pythagorean-comma/cv-module/docs/ASSUMPTIONS.md

# ASSUMPTIONS.md

Everything in this repo that had to be guessed, and what each guess costs if it is wrong.

Generated by `gen_assumptions.py`. The numeric entries are pulled from the code — `design.MEASURED`, `design.UNSPECIFIED`, `design.DEFERRED`, `contract.socket.ADAPTED` and `gen_bom.PRICES` — so a guess cannot be resolved in one place and left standing here. The rest are declared in that file, because a reading of a sentence does not fit in a dict of floats.

The discipline is the mixer's. Its `Assumption` class says it plainly: **the range matters more than the value.** The value is a guess; the range is a claim about what the design survives, and `check_assumptions()` fails the build if a value ever falls outside the range it was written around.

## The short version

**One entry would change the board; the rest would change a number:**

1. **`MEASURED['noise_floor']`** — the mixer's own unmeasured figure, which decides whether this module costs 0.11 dB or 0.85 dB with everything open, and 0.56 dB or 3.17 dB while the lead feature is running.

**The pad relay was the second and it is not an assumption any more.** It was the largest unchosen part in the design — 52 % of the placed courtyard, about two thirds of the BOM — and rather than being chosen it has been deleted, along with the pad it switched. `design.pad_benefit()` prices the pad against the control port that replaces it and the answer is 0.000 dB of system noise at every noise floor in the declared range. Nothing here is waiting on a relay.

**Two entries that *were* on this list are settled rather than open.** Constraint 2's "six separate returns" has been struck, with the arithmetic, in [Readings of the spec](#readings-of-the-spec). And the 20.2 µF that used to sit on VREF — twice the MAX6126's capacitive-load stability ceiling, because two 10 µF reservoirs were fitted — is resolved by deleting C804: its justification was shielding the reference's loop from an 8 kHz load step, and at 8 kHz a 10 µF could only supply 1.4 % of that step. VREF now carries 10.2 µF, which is the datasheet's own recommended 10 µF ∥ 0.1 µF, and `verify.check_reference_load()` holds the range against KiCad's netlist. See `design.reference_load()`.

## Numbers with declared ranges

From `design.MEASURED`, which is the mixer's `Assumption` class reused rather than reimplemented.

**8 of these are worth a bench and 2 are not**, and the difference is computed rather than felt. `design.SETTLED` names the ones whose *whole declared range* gives the same answer, and `design.check_settled()` recomputes that on every build — so a retirement expires the day the design makes one load-bearing again. Both of the retired ones are barrier residuals: at their joint worst corner, against the **optimistic** end of `noise_floor`'s own range, they put 4.09 µV at the audio bond, which is -21.8 dB — 1.8 dB inside the 20 dB the check holds, with three worst cases stacked.

### `cv_corner` = 254.7 Hz, 2-pole

**Range:** 200.0 .. 400.0

**Question:** Is a 250 Hz CV filter fast enough for the gate feel? Open question 5 in 00-current-state.md, and it is a judgement by ear rather than a measurement.

**Sets:** the anti-AM filtering, the de-click, and how the gate feels

**When wrong:** Two capacitors per channel. The corner scales as 1/C with the resistors fixed at the <=22k the noise budget wants, so 400 Hz is C1 = 36n / C2 = 15n and nothing else moves. Note the direction of the trade: faster is a worse anti-AM filter and a sharper click, and 00-current-state puts this block at 15-20 dB of the whole noise argument.

### `dcdc_node_v` = 40.0 V pk-pk, flyback primary switching node — **retired**

**Retired, and still a guess:** barrier_return() scales linearly with it, so the whole 24-72 V range moves the residual at the audio bond from 0.69 to 2.06 uV -- 46.4 dB to 36.9 dB *under* the mixer's own noise floor. There is no value in the range at which another part is worth fitting, which is the only decision it feeds.

**Range:** 24.0 .. 72.0

**Question:** How large is the swing on the TMR 6WI's primary switching node? A flyback's drain sits at Vin plus the reflected output, so at a 12-18 V input the range below is 2x to 4x the input -- read off what the topology permits, not off the datasheet, which does not say.

**Sets:** the common-mode current through the 50 pF barrier, and with it the size of the Y-capacitor

**When wrong:** Linearly. barrier_return() scales with it, so the top of the range is 5 dB worse than the value and the bottom is 4 dB better -- and the *fraction* returned locally does not move at all, because it is set by two impedances. What would change is whether the residual at the bond is worth another part, and at every point in this range it is not.

### `inlet_loop_uh` = 0.75 uH, the loop the shared inlet closes — **retired**

**Retired, and still a guess:** It used to be the denominator of a split and is a straight scale now: L801 puts 3.6 kohm in that denominator, so 0.3 and 1.5 uH return the same 99.984 % locally to five figures and differ only in the residual, 0.47 to 2.27 uV. **The choke is what retired it** -- before it was fitted the range mattered and the assumption's own when_wrong named a choke as the fix.

**Range:** 0.3 .. 1.5

**Question:** What is the inductance of the loop formed by the audio ground bond, the mixer's own AGND/PGND star, and the two inlet leads back to the shared barrel jack? It is a property of how the box is wired, not of either board.

**Sets:** the impedance of the bond the barrier's residual current is developed across

**When wrong:** **Re-read after L801 was fitted, and it is a different assumption now.** It used to be the *denominator of a split* -- barrier_return() divided the barrier current between C810 and this loop, so a smaller loop was a worse result and the whole declared range mattered. The choke puts 3.6 kohm in that denominator, so the split is set by the part and not by the box: 0.3 and 1.5 uH give the same 99.98 % local return to four figures. What is left is a straight scale on the residual, because the bond voltage is this impedance times a current that no longer depends on it -- a factor of 5 across the range, on 1.1 uV that is 42 dB under the mixer's own noise floor. Every point in the range is inaudible and so is every point outside it. The old clause named a choke as the answer if the number went the wrong way; the choke is fitted, so the question this assumption asks has stopped being load-bearing. **Retired: it is in SETTLED**, and it is the worked example of why that table needs check_settled() beside it -- this was load-bearing until one part went on, and would be again the day it came off.

### `logic_law_error` = 0.0023 fractional, '541 output-impedance asymmetry

**Range:** 0.0005 .. 0.01

**Question:** How different are the 74AHC541's output resistances high and low, at Vcc = 2.5 V? The asymmetry is a duty-dependent non-linearity in the control law, and the datasheet characterises VOH/VOL at 3.3 V and 4.5 V only.

**Sets:** the linearity of dB against code, and nothing else

**When wrong:** Nothing. It is common to all six channels -- same part, matched -- so it is a law error and not a matching error, and 0.23 % over a 61 dB span is 0.14 dB. Calibratable in firmware from a single measured curve if it ever matters.

### `mcu_dcdc_efficiency` = 0.85 fractional, TPS560430XF at 12 V in, 3.3 V out

**Range:** 0.75 .. 0.92

**Question:** What does U22 draw from VA_RAW at this board's real 3.3 V load? SLVSE22B gives efficiency as figures rather than as a table -- section 7.8's curves at 8, 12, 24 and 36 V in -- and a number read off a plotted curve is not a reading. The measurement is one ammeter in series with the switcher's VIN pin.

**Sets:** how much of the converter's remaining 128.2 mA of +Vout the controller costs -- it was the tightest budget on the board and it is not any more, which is what the note below is about

**When wrong:** **Only in one direction, and the threshold moved a long way when the fix it named was taken.** This read 'about 67 %', and the sentence after it named the lever: the 92.7 mA of relay coil V5 made linearly from twelve volts. That lever was pulled -- U22 makes 5 V now and carries the coils -- and it moved two things at once. The headroom before this block went from 35.4 mA to 128.2, because excluding the controller now excludes the coils too; and the coils stopped passing through the module's own converter, so there is no longer one number covering both stages. mcu_supply()'s u22_floor solves it: **53 % with the module at its own pessimistic end**, against a declared range starting at 75. The pessimistic corner fits with 37 mA of +Vout to spare, so what is left here is a confirmation and not a gate.

### `mcu_rail_ma` = 52.1 mA on 3.3 V, RP2040 alone, maximum average

**Range:** 19.2 .. 52.1

**Question:** What does the RP2040 draw on the 3.3 V side in *this* application? Its datasheet's Table 637 measures four use cases rather than specifying a maximum, and none of them is this one: 'Popcorn' is VGA video at 48 MHz and is the heaviest at 52.1 mA (DVDD 16.6 + IOVDD 35.5, worst-case device over temperature), 'BOOTSEL idle' the lightest active at 19.2 mA. This board runs 125 MHz with almost no IO activity -- six PWM at 30.5 kHz, one 10.4 MHz clock -- and XIP from flash, which Table 635 prices at 37.6 uA/MHz on DVDD and which firmware can retire by running from SRAM. The range is the datasheet's own measurements; the value is its top.

**Sets:** nothing, and that is the point -- controller_supply() shows the linear V3V3 chain fails at both ends of this range and a switcher clears both, so no topology decision waits on it

**When wrong:** Only the size of the switcher, not whether there is one. The bound that decides is conservation of energy: a converter's input current is at least vout/vin times its output, so 3.3/12 x 52.1 = 14.3 mA against 35.4 mA of +Vout headroom, and any efficiency above 40 % clears it. Measuring this would size a part; it would not change the topology. **Both halves of that held and the margin did not.** The switcher is fitted and mcu_supply() counts the rest of the rail -- the flash's 25 mA, the MIDI loop, the opto, the pedal -- so the 14.3 mA floor is 23.6 mA and the efficiency that clears it is 67 %, not 40. It still fits and it is the tightest margin on this board.

### `noise_floor` = 0.000144V rms

**Range:** 5e-05 .. 0.0004

**Question:** What is the residual noise at the mono output with the strings damped and LEVEL at maximum, unweighted over 20 kHz?

**Sets:** whether any further noise work on this box is worth doing

**When wrong:** Near the predicted figure means the source model in source.py is right and the summer is already 29 dB below the thing feeding it. Much lower means the assumed coil resistance and rbb' are pessimistic. Much higher means something is wrong that this model does not describe.

### `pico_smps_efficiency` = 0.91 fractional, RT6150 at 4.7 V in, 3.3 V out, PWM

**Range:** 0.86 .. 0.93

**Question:** What does the Pico draw from VSYS at this board's load? DS6150A/B-05 gives efficiency only as plotted curves -- the 'Buck-Boost 3.3V Efficiency, PS/SYNC = H' figure, which is the forced-PWM one this design runs in -- and at 100 mA the VIN = 3.3 V trace sits near 95 % with the 2.4 V trace about three points under it. A number read off a plotted curve is not a reading, and this one is read at a different inductor from the module's. The measurement is one ammeter in series with the Pico's VSYS pin, with GPIO23 high.

**Sets:** what the module's own 3.3 V load costs +Vout, which is 43 % of what U22 delivers -- see mcu_supply()

**When wrong:** **It is not a threshold on a product and it never was.** This read 'the product with the other assumption's floor is 0.660, and 0.678 is where the budget stops closing'. 0.678 was mcu_supply()'s single-stage conservation floor carrying a second name -- the same expression, called a product -- so the framing was wrong before the number was. The topology then made it wrong twice: **57 % of VMOD's power is relay coil**, which passes through U22 and never through this converter, so the two stages are not in series for most of the load and no product describes them. mcu_supply()'s module_floor is the honest figure -- **45 % with U22 at its own pessimistic end**, against a declared range starting at 86. Nothing here gates the design; the measurement is worth taking because a curve read off a figure is not a reading.

### `servo_vos` = 0.0005 V, servo amplifier input offset

**Range:** 5e-05 .. 0.003

**Question:** What input offset voltage does the servo amplifier actually have? The residual DC on SIN{n} is this figure and almost nothing else -- the loop drives its own offset to the output.

**Sets:** the DC this module leaves on SIN{n}, and therefore whether constraint 3 holds

**When wrong:** See servo_residual(). What the constraint actually protects is DC *current* through the mixer's master wiper, and C703 turns 3 mV at SUM_OUT into 3 nA there -- the same order as the 0.2-1.0 nA the mixer already accepts from its own op-amp. Even the top of this range is comfortable. If it were not, the answer is a zero-drift part in the servo and not a series capacitor: a capacitor would put a second high-pass within a decade of the mixer's own 15.9 Hz, which is what its DC_BLOCK_VALUE comment warns against.

### `vca_rin` = 12100.0 ohm, R_IN = R_OUT, one fixed pair per channel

**Range:** 7500.0 .. 20000.0

**Question:** How low can R_IN go before distortion costs more than the noise it buys? The datasheet gives a range and a direction -- 7.5k to 100k, 'lower values will produce the best noise performance at some cost in distortion' -- and no number. The one figure it does give is the level dependence: 0.05 % at 0.775 V rms and 0.025 % 17 dB below that.

**Sets:** the VCA's output noise, and with it whether this module is audible against the six Nu capsules at all

**When wrong:** Nothing structural: two resistors per channel, same footprint, and the coarse pad's deletion means the top of the range is no longer bounded by anything but the part. **Decided rather than left open, and the trigger is a number.** The old text here said the choice was 'worth 0.3 dB at the predicted 144 uV and 0.8 dB at the optimistic end' -- delta.rin_sensitivity() computes **0.04 dB quiescent and 0.20 dB while gating** at 144 uV, and 0.26 / 0.92 dB at 50, so the old pair was the gating figures rounded and read as though they were the quiescent ones. So R_IN stays at 12k1, against a distortion cost page 4 gives a direction for and no number -- and **revisit at 81 uV**, which is the measured floor at which 7.5k first reaches half a decibel in the lead feature. Downstream of one meter reading and of nothing else.

## Inherited from the mixer

Facts this repo takes from `../summing-mixer` at `4bc7ddb`. Their truth is upstream's problem; what is assumed here is only that they still apply.

| | value | upstream | quoted |
|---|---|---|---|
| `AMBIENT_C` | `(0.0, 50.0)` | `design.DIELECTRICS (comment)` | "X5R and X7R differ only in temperature range and both are class II, so both are accepted; a pedal never leaves 0-50 C." |
| `GROUND_STAR` | `R901` | `design._GROUND_RULE` | "AGND and PGND meet at exactly one component, R901, and nowhere else." |
| `WIPER_WORST_OHMS` | `2500.0` | `design.summing_stage_noise` | "It peaks at pot/4 = 2500 ohms at half rotation and is zero at both ends." |
| `MOUNTING_IS_ISOLATED` | `True` | `design.mounting` | "Four plated holes would therefore be four more bridges between AGND and PGND running in parallel with R901." |

`AMBIENT_C` is the one that does work here: 0–50 °C is what decides that the SSI2164's −3300 ppm/°C drift is not worth compensating, and it comes from a comment in the mixer about ceramic dielectrics — *"a pedal never leaves 0-50 C"* — rather than from anything about this module.

## Parts not chosen

None. The one entry was the pad relay — a part the spec asks for by function, does not name, and §6 forbids inventing — and it was resolved by deleting the pad rather than by choosing the relay. See `design.pad_benefit()`. `design.check_orderable()` and `check_pin_numbers()` are unchanged and still refuse a BOM line with no part number and a pin written as a role; the deferred DC-DC, ADC and bypass relay will refill this list when they are drawn.

## Blocks deferred

Not assumptions so much as absences, listed because a section 5 check against a partial board proves less than it appears to.

### Pins waiting on a deferred block

None. All 48 were the twelve pad relays' coils, and they went with the pad — see `design.pad_benefit()`. `verify.check_open_pins()` still holds the declaration in both directions, so a pin left open on the sheet and declared nowhere still fails; there is simply nothing declared as waiting.

**Section 4.5's coil arithmetic is resolved by subtraction, and it is worth keeping what it said.** It asked for "12 coils (six 2-bit pads)" driven by "2 × TPIC6B595" — 16 outputs. Twelve coils is twelve *single*-coil relays, and a single-coil latching relay latches by reversing its coil polarity, which needs a bridge; the TPIC6B595 is an open-drain sink and cannot reverse anything. With the dual-coil latching part section 4.1 asks for, six 2-bit pads are 12 relays and **24 coils, which is 3 × TPIC6B595 exactly**. The contradiction was real and it is now moot: there are no coils, no drivers, no one-shot and no coil supply rail. It is recorded because a spec that does not close arithmetically is worth knowing about even when the block it describes has been deleted.

## Readings not taken

### The MAX6126's turn-on settling time, and the fail-safe sequence.

**Basis:** Read first-hand (page 4, and page 16 in prose): turn-on to 0.01 % of final value is 1 ms with no NR capacitor and **20 ms with the 0.1 uF fitted**. The capacitor is fitted, for 75 -> 45 nV/rtHz.

**Affects:** The power-up sequence, which spec section 4.5 says to "design explicitly" and nothing in this repo had a number for. The '541's Vcc *is* VREF, so for 20 ms after power-up every channel's full scale is ramping from zero -- and positive Vc attenuates, so zero CV is unity gain. Section 4.5's named hazard, arriving by the reference rather than by the DAC.

**If wrong:** Nothing, if the bypass relay is held bypassed across it: 20 ms is 4x the ~5 ms section 4.5 quotes for a relay to transfer, so the margin is comfortable. It is a sequencing requirement rather than a hazard. If it is *not* sequenced, the box is briefly at unity gain on all six strings at power-up, which is the loudest possible failure.

**To settle:** Nothing to settle -- the figure is read. It belongs in the fail-safe block, which is DEFERRED, and design.VREF_TURN_ON_S is where it is waiting.

### The OPA1644's input offset voltage.

**Basis:** Not read. `MEASURED['servo_vos']` assumes 0.5 mV with a declared range of 0.05 to 3 mV, which is wide enough to cover any JFET quad.

**Affects:** The residual DC on SIN{n}, which is constraint 3.

**If wrong:** Nothing, across the whole declared range: servo_residual() shows the worst case still lands at nanoamps through the mixer's master wiper, against the 0.2-1.0 nA it already accepts.

**To settle:** One line of the OPA1644 datasheet. Worth doing when the BOM is finalised anyway.

### The 74AHC541's output impedance at Vcc = 2.5 V.

**Basis:** The datasheet characterises VOH/VOL at 3.3 V and 4.5 V only. `MEASURED['logic_law_error']` extrapolates.

**Affects:** The linearity of dB against code -- a duty-dependent bend in the control law.

**If wrong:** Nothing structural. It is common to all six channels, so it is a law error rather than a matching error, and 0.23 % over a 61 dB span is 0.14 dB. Calibratable in firmware from one measured curve.

**To settle:** Measure V_C against duty on one channel, once.

## Modelling assumptions

### The SSI2164's output noise is flat across the band.

**Basis:** The datasheet publishes four points in dBu over 20 Hz to 20 kHz unweighted, and no spectrum at all. vca_noise() converts a total to a density by assuming it is flat.

**Affects:** Every noise figure this repo quotes for the VCA, and therefore the whole of delta.py's system arithmetic.

**If wrong:** If the part has significant 1/f, the density at low frequency is higher than modelled and the figures are optimistic where the instrument's fundamentals are.

**To settle:** A spectrum analyser on one channel at Phase 1. This is worth adding to the phase-1 bench list, which currently only has feedthrough, noise and law drift on it.

### How much of the SSI2164 cell's noise sits ahead of its gain core.

**Basis:** vca_cell_fit() splits the datasheet's four points into a current at the cell's output and a fixed voltage there, but not into input-referred and output-referred parts -- nothing in the datasheet distinguishes them, and it publishes no noise-against-gain figure at all. design.cell_noise() takes it as a parameter with no default.

**Affects:** How much quieter a shut channel is than an open one, which is most of the gating penalty in delta.system_delta(): at the pessimistic end the cell's noise does not attenuate at all, and the penalty at the optimistic noise floor is 2.9 dB against 1.8 dB at the other end.

**If wrong:** Nothing about the board. Both ends were computed before the coarse pad was struck, precisely so the decision would not depend on this -- and it does not, because the pad loses at both.

**To settle:** A noise measurement at two gain settings on one channel, at Phase 1. It belongs on the same bench visit as the feedthrough test.

### The SSI2164 noise table already includes an I-V amplifier.

**Basis:** The specification conditions say 'using Figure 1 circuit without diode', and Figure 1 contains a 1/2 TL072 and both resistors. So channel_noise() adds no separate I-V term.

**Affects:** Whether delta.py double-counts the largest contributor.

**If wrong:** If the figure is somehow the cell alone, this repo *under*-counts by an op-amp and a resistor -- about 15 nV/rtHz, which would raise the gating penalty by roughly 0.1 dB.

**To settle:** It is a reading of the conditions line and it is a confident one. Left as an assumption because it is load-bearing, not because it is doubtful.

### A bowed onset is slower than a picked one, and never faster.

**Basis:** The target instrument is a modern arpeggione -- six strings, standard guitar tuning, bowed as well as picked -- and no bowed envelope is measured anywhere in this project. hexsim's only measured profile is a picked electric, and its sustained_stems() models an ebow-like source with a 0.6-1.5 s swell rather than a bow.

**Affects:** Nothing, and that is the point of recording it. envelope_filter() is bounded above by the *picked* transient and below by ripple, so a bow that rises more slowly only ever asks for more smoothing than tau already gives. If a bowed attack were somehow faster than 20 ms the bound would move, and nothing else in the block would.

**If wrong:** The detector would read a bowed onset late by up to a few milliseconds, which is inside the 8 ms the firmware averages over anyway.

**To settle:** Record one bowed note off the Nexus at Phase 0.5 and run it through hexsim --stems. It is the same recording session the picked stems need.

### The musical attack and release belong in firmware, not in the RC.

**Basis:** envelope_filter() shows a symmetric 4.7 ms one-pole falls 46x faster than the fastest musical decay, so there is no release the analogue side has to be asked for. Bowed and picked want opposite shaping and the instrument does both, which a fixed RC cannot serve and a constant at the 2 kHz frame can.

**Affects:** Where a musical decision lives. The board is identical either way; what changes is whether the decision costs a soldering iron.

**If wrong:** If firmware shaping turns out not to be enough -- a case nobody has described -- the fallback is a diode and a second resistor per channel, which is the asymmetric detector spec section 4.4 implies. It is two parts per channel, added later, on a board that already has the sections.

**To settle:** Set it by ear against hexsim's renders, which is how corrections 7 and 8 were found. It needs no hardware.

### The Schottky forward drop at the *pump*, which is the half of this that is still an assumption.

**Basis:** PUMP_DIODE_VF = 0.32 V for the BAT54 at D801/D802. The datasheet has now been read (DS11005 Rev. 34-2) and its lowest tabulated point is 240 mV **max** at 0.1 mA; the pump's hold node is bled at about 18 uA, an order of magnitude below that, where the table stops. So 0.32 V is not a reading -- it is a deliberate pessimism sitting above the datasheet's own maximum at ten times the current, in the style OUTPUT_SWING_MARGIN uses upstream.

**Affects:** pump_timing()'s margin only. The gate reaches 3.3 - 2*Vf before the bleed divides it, so a *smaller* Vf gives more gate voltage: every direction the real part can move is the safe one, which is why this is now a comfortable assumption rather than the tightest in the repo.

**If wrong:** The gate is computed at 1.83 V against a 1.0 V threshold requirement. At the datasheet's 0.24 V it would be 1.99 V, and at 125 C lower still -- Figure 1 of the PMEG data sheet shows the tempco is negative, so a hot junction *helps* here. **The old entry said the opposite** -- "the direction that hurts is the one a hot junction moves in" -- which is true of a silicon junction's leakage and false of a Schottky's forward drop.

**To settle:** Nothing, before ordering. If the pump is ever measured short of gate, the reading to take is Vf at 20 uA, which is off the bottom of the published table and would have to be measured rather than read.

### **RESOLVED** -- the clamp's forward drop, which used to share the entry above and was the assumption in this repo with the least slack behind it.

**Basis:** It is read now, not assumed, and reading it found the clamp did not work. Two things were wrong. The current was stated as "the microamps this circuit draws" and D803 sits on U8's output pin, so it carries the amplifier's short-circuit current -- 36 mA, from SBOS484D page 8. And the BAT54's own table gives 500 mV max at 30 mA, which is +13.4 dB: over the mixer's headroom by 5.5 dB, on the fault the clamp exists to prevent.

**Affects:** Nothing now. clamp_gain() computes the drop from the fitted part's datasheet at the current clamp_current() derives, so the number is a result rather than an input.

**If wrong:** The fix is a part, not a resistor, and clamp_current() shows why: the normal reference load and the fault current cross the same series resistor, so their ratio is 4.54x whatever its value. A PMEG2010AEH -- a 1 A die run at 36 mA -- is 259 mV max there, which is +6.3 dB with 1.5 dB of margin.

**To settle:** Settled. What is left is a requirement rather than a guess: clamp_vf_ceiling() states it as 0.32 V at clamp_current(), and any substitute part is checked against that.

### **RESOLVED** -- a 5 V signal DPDT relay coil draws 25-40 mA.

**Basis:** It was an envelope for the class, because the relay was in design.UNSPECIFIED. The relay is an Omron G6S-2 DC5 now and its own ratings table gives 28.1 mA on 178 ohm at 5 VDC, to a stated +-10%.

**Affects:** coil_budget(), and through it the deferred supply. The figure it carries is 76 to 93 mA continuous on V5 rather than 75 to 120, against 78 mA for every amplifier and VCA on the board -- so the supply's largest single load is now a read number and not a guess.

**If wrong:** Nothing. The band it replaces contained it.

**To settle:** Settled by choosing the part. What it leaves behind is a requirement on the one block still deferred: the supply has to hold 5 V through 93 mA of coil plus the reference's own draw, and design.coil_budget() is where that number lives.

### X7R is acceptable for the CV filter's 56 nF and 22 nF.

**Basis:** Assumed, not computed. At 2 V on a 50 V part the bias derating is a few per cent and f0 goes as 1/sqrt(C1 C2), so the corner moves a per cent or two.

**Affects:** The CV filter's corner and Q, and therefore the anti-AM figure.

**If wrong:** Nothing audible: a 2 % shift on a 255 Hz corner. The reason it is recorded is that this design names C0G explicitly everywhere it matters, and these two are the only signal-adjacent parts that are not C0G -- because C0G at 56 nF is a much larger package.

**To settle:** Compute the bias curve for the specific part, or fit film and take the area.

### Courtyard areas and a packing factor of 2.5.

**Basis:** The areas are from the footprint names; the packing factor is a judgement. The 14 x 9 mm relay envelope that used to be the largest term is now only in floorplan.pad_area(), which prices what was deleted rather than what is fitted.

**Affects:** floorplan.area(), and with the pad gone the finding has reversed: 3310 mm2 against the mixer's own 6189 mm2 outline, where it was 7225 and 1036 mm2 short.

**If wrong:** The reversal survives a wide error -- it is a factor of 1.9, not a few per cent -- but the deferred blocks are not in it, so 'fits' means 'has stopped being obviously too big'.

**To settle:** Place the deferred blocks. The packing factor is only worth arguing with once there is an outline to argue about.

## Firmware assumptions

### Firmware emits the complement of the level.

**Basis:** Required by 'code 0 = loudest' with the datasheet's Figure 10 topology: V_C is the *difference* between V_REF and the '541's output, so the loud end is 100 % duty.

**Affects:** Nothing in hardware -- the board is identical either way. Only which direction a firmware variable counts.

**If wrong:** The control law runs backwards. Obvious in a second at the bench.

**To settle:** One line, and it is written down here because it is the kind of thing that gets lost between a schematic and a firmware repo.

### The six PWM slices can be phase-staggered.

**Basis:** Spec section 4.2 asks for it and the RP2040's PWM slices have independent counters, so it should be available. Not verified against the datasheet or the SDK.

**Affects:** The reference's transient load: staggering divides the peak by six.

**If wrong:** Little. The arithmetic in REFERENCE_PLACEMENT shows the transient is 19 uA against the MAX6126's 10 mA, so the stagger is a free improvement rather than a requirement.

**To settle:** Check the RP2040 datasheet when the controller block is drawn.

## Readings of the spec

### Constraint 2's "six separate returns to six pin-3s" has been **struck**, not interpreted.

**Basis:** It was generated in an earlier session answering a question about power, not derived from a measurement or a datasheet, and was then written into CLAUDE.md under "load-bearing constraints" -- which is what made it unquestionable. Per-channel returns exist to prevent shared-impedance crosstalk; computed for this module with a single bond carrying all six channels, pairwise crosstalk is 122 dB below one string on a 100 mm bond and 103 dB on a deliberately bad one, against a -54 dB requirement.

**Affects:** The front-end topology. It was a four-resistor difference amplifier to satisfy the clause literally; it is now a two-resistor inverting stage, and the loom is a shielded pair rather than a triad.

**If wrong:** Nothing measurable either way -- the two topologies differ by 0.008 dB of system noise, because the VCA's 62 nV/rtHz swamps the front end. What was at stake was twelve resistors and a matched-set requirement, spent to satisfy a sentence with no mechanism behind it.

**To settle:** **Settled.** The half of the constraint that has a mechanism -- exactly one bond, which is the mixer's own _GROUND_RULE applied across the connector -- is kept and checked. The half that does not is gone, and design.FRONT_R carries the arithmetic. Constraint 5's "triad" becomes "twisted pair inside an individual shield".

### The ground bond lands on the mixer's TP6.

**Basis:** TP6 is the mixer's own AGND test pad and its comment calls it 'the *only* correct one, given the ground rule'. Nothing in the mixer designates a bond point, because nothing was expected to bond to it.

**Affects:** Where one wire is soldered, and the loom's geometry.

**If wrong:** Any AGND point works electrically. TP6 is chosen because it is the one the mixer itself designates.

**To settle:** Its coordinates are not in fab/mechanical-summing-mixer.json -- test pads are not tall parts -- so they have to be read off the board or the .kicad_pcb before the loom is made.

### The six triad shields land at the bond point too.

**Basis:** Constraint 5 says shields are grounded at the main-board end only and does not say where. Grounding them at the bond keeps every shield at the same potential as the module's own reference.

**Affects:** The loom's construction.

**If wrong:** Grounding them at six separate pin-3s would work too, and would put six shield currents into six different points of the mixer's AGND pour. The single point is the more conservative choice.

**To settle:** A loom decision, not a board one.

### 3 + 3 across the two SSI2164 packages, not 4 + 2.

**Basis:** Crosstalk is a within-die property and is the binding constraint on the lead feature. 3 + 3 gives every string two die-mates; 4 + 2 gives four strings three and two strings one.

**Affects:** Which channel is which cell, and the floorplan.

**If wrong:** Nothing measurable until Phase 1.5 measures crosstalk. If it comes back far better than -54 dB the arrangement stops mattering.

**To settle:** Phase 1.5, which is already on the staging list for exactly this.

### Op-amp sections are grouped by block, not by channel.

**Basis:** Four sections per channel would put one quad per channel, which is tidy and puts a 30.5 kHz CV filter on the same die as an audio front end. Grouping by block keeps them apart at the cost of eight packages with one spare section.

**Affects:** design.SECTIONS, and the floorplan's zone layout.

**If wrong:** Provisional. This is the one table in design.py the floorplan may move, and moving it changes no values.

**To settle:** Settled when the board is laid out.

## Supply

### The module's audio rails are +/-12 V.

**Basis:** Spec section 1.1 decides the topology -- isolated DC-DC at >=300 kHz, +/-12 V for a small audio domain -- and the DC-DC part is not chosen.

**Affects:** die_rise(), which is 118 C/W x 24 V x 6 mA = 17 C, and therefore the tempco span. Also the CV filter op-amp's ability to output exactly 0 V, which needs a negative rail.

**If wrong:** A lower rail lowers the die temperature and narrows the tempco span, which is the direction that helps. A single supply would break the 0 V requirement outright.

**To settle:** Choose the DC-DC. Note the SSI2164 spans +/-4 to +/-18 V, so the rail is not tightly constrained by the VCA.

### The offset reference is stable enough.

**Basis:** Rossum's Note 3 wants the negative reference 'temperature stable to 100 ppm/degC'. This design inverts the +2.5 V reference through one op-amp section and two 0.1 % resistors, and the resulting drift has not been computed.

**Affects:** The zero point of the control law -- what V_C is at the loud end, and therefore whether unity gain is really unity.

**If wrong:** A common-mode gain error, not a matching error, because all six channels share the one inverted reference. Probably invisible; unverified.

**To settle:** Compute the inverter's drift from the resistors' tempco and the op-amp's, against the 100 ppm/degC Note 3 asks for.

## Prices

Of 63 BOM lines, **6 carries a price read from a page fetched in this session**. 2 come from search results quoting a distributor without the page being opened, and 55 are typical bands for the class — estimates, labelled as such in the `basis` column of `out/cv-module-bom.csv`.

The totals in `docs/SHOPPING.md` are therefore a range, and the range is honest rather than decorative. They are also a floor: none of the deferred blocks is costed.

## What is not assumed

For contrast, because a document of guesses can make a design look less settled than it is. These were derived or read, and each has its arithmetic in the repo:

- The **control law** — −33 mV/dB, the 9k:1k divider, the 9/10/11 kΩ tolerance and dg/g = −3.488 per volt, all from the datasheet, with the constant re-derived from q/kT to 2.4 %.
- **Class AB** — pin 1 open, from three separate statements in the datasheet, worth 12 dB and better control feedthrough.
- **V_REF ≤ 4.71 V** — from the '541's VIH against a 3.3 V GPIO. This is what rules out the 5 V reference and it is arithmetic, not preference.
- **R_OFF = R1** — the exact-cancellation condition, not a value.
- **The CV chain is fail-silent** — every fault drives the '541 output toward 0 V, which is full attenuation, because the offset current comes from neither the MCU nor the reference that feeds it.
- **The MAGND star is at the SSI2164 ground pins** — because the control port is ground-referenced, so 1 mV in the wrong place is AM 51 dB below the signal.
- **The five section 5 constraints** — checked mechanically by `verify.py`, and `test_verify.py` plants 27 faults to prove the checks can fail.
- **Every pin map in the netlist** — SSI2164, OPA1644, SN74AHC541 and now the MAX6126, each read off its own pin-configuration table. The MAX6126 was the last one out: it had been read from a text mirror, three comments and this document went on saying it had not been read at all, and it is now confirmed pin-for-pin against Maxim's own PDF. The mirror was right.
