pythagorean-comma/cv-module/gen_pcb.py

"""Build the board for the design in design.py, through KiCad's own pcbnew.

    python3 gen_pcb.py

**Run it with the ordinary interpreter; it re-runs itself under KiCad's.**
`pcbnew` is a SWIG extension that only exists inside KiCad's bundled Python, so
this file starts as a launcher and finishes as a board generator. The mixer
solves the same problem with a `build.sh`; this repo's README is a chain of
`python3 x.py &&` and keeping that shape is worth eight lines of re-exec.

**The deprecation is a schedule, not a defect**, per CLAUDE.md: there is no
official API for boards, the IPC one is PCB-focused but not shipped for this,
and the SWIG bindings are what the sibling repo's fabricated boards came out
of. When removal lands it is a problem for both repos at once.

Two things it does that are not obvious and are both the mixer's hard-won
lessons, read at the pin:

**SaveBoard() writes the project file too**, through KiCad's settings manager,
and what it writes there is KiCad's *defaults* -- so every design rule
gen_project.py sets is gone the moment this saves. The mixer's build.sh re-runs
its project generator afterwards for exactly that reason and says several hours
were spent chasing violations that were only that. This file re-runs
gen_project.py itself, after saving, and check_rules() in verify.py is what
stops the discipline from decaying into a comment.

**Footprints are placed with their library nickname restored.**
`pcbnew.FootprintLoad()` returns the footprint under its bare name; without
`SetFPIDAsString()` KiCad cannot tie it back to a library and "Update
Footprints from Library" has nothing to work from.

**This file places and pours. It does not route, and that is the decision this
pass took rather than the limit it started from.** route.py -- a maze router
with rip-up and retry, a fan-out for fine pitch and a three-way via exclusion
model -- closed this board at 0 unrouted and 0 DRC, and it is deleted. The
problem it existed for went with the RP2040's QFN-56; what it cost, and this
is the part worth carrying, was that the *board* had to be a function of
design.py, so no question about geometry could be asked of a layout until it
had been answered in Python first.

**So the board is edited from here -- by a person in KiCad, or by a scoped
krt.py run -- and this file will destroy that copper if it is run again.** It
writes a fresh board with the footprints placed and the planes poured and
nothing else on it; pcbnew has no notion of "the parts moved, keep the
tracks". The sync path for a netlist change is KiCad's own
**Update PCB from Schematic**, against the generated out/cv-module.kicad_sch.
The rule, stated the same way here and in CLAUDE.md and README.md because one
copy is the wrong number for this one:

    **the netlist is generated and authoritative; the board is not
    regenerated -- it is edited, and verified by reading it back.**

What this pass does and does not do:

  * places every part at placement.py's coordinates, with every pad on its net
    from design.py;
  * reserves a courtyard for each part that has no footprint because it is not
    chosen -- there are none left, and the mechanism stays;
  * draws the outline that placement.extents() derives, and the two ground
    zones either side of the split;
  * stitches every ground pad to the plane under it, because a plane
    connection is not routing: it is a hole to the copper already underneath,
    and it is the one piece of geometry a person laying this board out would
    otherwise have to reproduce 100 times by hand;
  * **lays no signal copper at all.**
"""

import math
import re
import os
import pathlib
import subprocess
import sys

HERE = pathlib.Path(__file__).resolve().parent
OUT = HERE / "out"
# Declared up here rather than beside FOOTPRINT_DIR, where it used to be:
# _relaunch() runs before that point and needs the board's path to write the
# stackup into it after the child process has saved.
PROJECT = "cv-module"
BOARD = OUT / "cv-module.kicad_pcb"

# Design rules, and **they are not here any more.** They were, with a comment
# claiming "gen_project.py imports them so the two cannot disagree" -- and
# gen_project.py could not import them, because importing this file relaunches
# it under KiCad's interpreter before any constant is reachable. So it wrote
# its own copies as literals and the two agreed by hand. rules.py is the one
# copy now, it derives the routing pitch rather than asserting it, and
# verify.check_rules() reads the project and the board back off disk to hold
# all three together. That check was named in this docstring before it
# existed; see rules.py.
sys.path.insert(0, str(HERE))
import rules                                                      # noqa: E402
import gen_pcb_guard                                              # noqa: E402

TRACK_MM = rules.TRACK_MM
CLEARANCE_MM = rules.CLEARANCE_MM
VIA_DIAMETER_MM = rules.VIA_DIAMETER_MM
VIA_DRILL_MM = rules.VIA_DRILL_MM
EDGE_CLEARANCE_MM = rules.EDGE_CLEARANCE_MM

# **Empty, and the reserve() machinery below is kept.** This carried a 14 x 9 mm
# envelope for each bypass relay while design.BYPASS_RELAY was None. Both
# UNSPECIFIED parts are chosen now, so all 225 parts have a footprint and
# nothing is reserved -- but a repo that defers blocks will reserve area again,
# and what is worth keeping is the mechanism rather than this instance of it.
RESERVED_MM = {}


def _relaunch():
    """Re-run this file under KiCad's bundled Python, then fix the project."""
    sys.path.insert(0, str(HERE))
    from toolchain import kicad

    interpreter = kicad.BUNDLED_PYTHON
    if interpreter is None:
        raise SystemExit(
            "pcbnew lives in KiCad's own Python and this install does not "
            "bundle one.\nOn Linux, run: python3 -c 'import pcbnew' to check, "
            "then invoke this file with whichever interpreter has it.")
    result = subprocess.run([str(interpreter), str(HERE / "gen_pcb.py")]
                            + sys.argv[1:],
                            env={**os.environ, "CV_PCB_CHILD": "1"})
    if result.returncode != 0:
        raise SystemExit(result.returncode)

    # SaveBoard() has just overwritten the project with KiCad's defaults.
    print("  re-running gen_project.py: SaveBoard() rewrote the project")
    again = subprocess.run([sys.executable, str(HERE / "gen_project.py")],
                           capture_output=True, text=True)
    if again.returncode != 0:
        raise SystemExit(again.stdout + again.stderr)

    # **And the stackup, for the same reason one line up.** pcbnew can set it,
    # and setting it there would mean it could only ever be written by the one
    # generator that cannot run on a routed board -- so it is written to the
    # file instead, by rules.apply_stackup(), which works on a board this file
    # just made and on one somebody has since edited. verify.check_stackup()
    # is what holds the two together.
    if rules.apply_stackup(OUT / f"{PROJECT}.kicad_pcb"):
        print("  wrote rules.FAB_STACKUP into the board")


if os.environ.get("CV_PCB_CHILD") != "1":
    _relaunch()
    raise SystemExit(0)

# ---------------------------------------------------------------------------
# From here down, this is running under KiCad's interpreter.
# ---------------------------------------------------------------------------

import pcbnew                                                    # noqa: E402

sys.path.insert(0, str(HERE))
import design as circuit                                         # noqa: E402
import placement                                                 # noqa: E402
from toolchain import kicad                                      # noqa: E402
from toolchain.kisch import _uuid as symbol_uuid                 # noqa: E402

FOOTPRINT_DIR = kicad.FOOTPRINT_DIR
# The project's own footprint library, written by gen_project.py, holding the
# one land pattern KiCad does not ship. Resolved here rather than by copying
# the file into KiCad's installation, which is the same argument gen_project
# makes for `${KIPRJMOD}` in fp-lib-table: a build that writes into the
# toolchain is a build that cannot run on another machine.
PROJECT_LIBS = {"cv": HERE / "out" / "cv.pretty"}


# **Which side a piece of copper is on.** Local again, which is where they
# were during the pass route.py did not exist. They were the router's own
# constants while it was here, on the argument that pad_boxes() handed its
# boxes straight to route_all() and two notions of "front" between two files
# is the class of fault this repo keeps finding -- true, and it needed a
# second file to be true of.
#
# **The reason they stay at all is stitch_grounds().** The claim beside them
# used to be that "verify.py's geometric checks read the boxes"; verify.py
# imports nothing from this file and reads the *board*, so pad_boxes() has
# exactly one consumer left and it is one file away. A via stitching a ground
# pad is copper on both signal layers and has to say so.
FRONT, BACK = 0, 1
LAYERS = (FRONT, BACK)


def point(x, y):
    return pcbnew.VECTOR2I_MM(float(x), float(y))


class Board:
    """One board out of design.py, built by placing and pouring."""

    def __init__(self, layers=4):
        self.board = pcbnew.BOARD()
        self.board.SetCopperLayerCount(layers)
        self.nets = {}
        self.footprints = {}
        self.courtyards = []
        self._owner = circuit.DESIGN.pin_owner()
        for name in sorted(set(self._owner.values())):
            net = pcbnew.NETINFO_ITEM(self.board, name)
            self.board.Add(net)
            self.nets[name] = net

    def net(self, name):
        return self.nets[name]

    def place(self, ref, x, y, rotation):
        part = circuit.PARTS[ref]
        library, name = part.footprint.split(":", 1)
        directory = PROJECT_LIBS.get(library,
                                     FOOTPRINT_DIR / f"{library}.pretty")
        footprint = pcbnew.FootprintLoad(str(directory), name)
        if footprint is None:
            raise SystemExit(
                f"could not load footprint {part.footprint} for {ref} from "
                f"{directory} -- check the name against KiCad's own library, "
                f"or against gen_project.footprint_library() if the nickname "
                f"is a project one")
        self.board.Add(footprint)
        footprint.SetFPIDAsString(part.footprint)
        # The same UUID gen_sch.py derived for this symbol, so the two files
        # describe one part rather than two. Without it, "Update PCB from
        # Schematic" treats every footprint as new.
        footprint.SetPath(pcbnew.KIID_PATH(
            f"/{symbol_uuid(f'{PROJECT}:part:{ref}:1')}"))
        footprint.SetReference(ref)
        footprint.SetValue(str(part.value))
        footprint.SetPosition(point(x, y))
        # **Designators for two-terminal parts go on F.Fab, not on silk.** This
        # board has 128 of them on a 4 mm pitch, and their reference text is
        # wider than the part: KiCad's DRC reported thirteen silkscreen
        # collisions on the first clean placement and every one was a
        # designator, not a part. F.Fab is where an assembly drawing reads them
        # from anyway; what silk is for is the parts a human orients by hand,
        # which is the ICs and the connectors.
        #
        # **The test was `len(footprint.Pads()) <= 2` and that is a proxy for
        # the intent, not the intent.** Moving five BAT54s from SOD-123 to
        # their real package took them from two pads to three -- a SOT-23 has
        # a pin 2 that is not connected -- so the rule stopped applying, five
        # designators were promoted onto silk, and DRC reported 12 silkscreen
        # collisions among parts that had not moved a micron. The part is
        # exactly as small as it was; what changed was a number the rule was
        # reading instead of the thing it meant.
        #
        # So it counts the terminals the *design* connects, which is what
        # "two-terminal part" means and is a fact about the circuit rather than
        # about a land pattern. Q801's SOT-523 has three connected pins and
        # keeps its designator on silk, which is right: a transistor is
        # oriented by hand.
        connected = sum(1 for pad in footprint.Pads()
                        if (ref, pad.GetNumber()) in self._owner)
        if connected <= 2:
            footprint.Reference().SetLayer(pcbnew.F_Fab)
        if rotation:
            footprint.SetOrientationDegrees(float(rotation))
        move = placement.REFERENCE_MOVES.get(ref)
        if move:
            text = footprint.Reference()
            here = text.GetPosition()
            text.SetPosition(pcbnew.VECTOR2I(
                here.x + pcbnew.FromMM(move[0]),
                here.y + pcbnew.FromMM(move[1])))
        for pad in footprint.Pads():
            key = (ref, pad.GetNumber())
            if key in self._owner:
                pad.SetNet(self.net(self._owner[key]))
        self.footprints[ref] = footprint
        box = footprint.GetCourtyard(pcbnew.F_CrtYd).BBox()
        self.courtyards.append((
            ref,
            pcbnew.ToMM(box.GetLeft()), pcbnew.ToMM(box.GetTop()),
            pcbnew.ToMM(box.GetRight()), pcbnew.ToMM(box.GetBottom())))
        return footprint

    def reserve(self, ref, x, y, width, height):
        """Commit board area to a part that is not chosen yet.

        A rectangle on User.Drawings and an entry in the courtyard list, so the
        outline and the overlap check both see it. **This is design.UNSPECIFIED
        made physical**: the schematic can carry a part whose pins are known and
        whose part number is not, and so can the board -- what it cannot carry
        is a hole where nobody remembered anything goes.
        """
        left, top = x - width / 2, y - height / 2
        right, bottom = x + width / 2, y + height / 2
        corners = [(left, top), (right, top), (right, bottom), (left, bottom),
                   (left, top)]
        for start, end in zip(corners, corners[1:]):
            shape = pcbnew.PCB_SHAPE(self.board)
            shape.SetShape(pcbnew.SHAPE_T_SEGMENT)
            shape.SetStart(point(*start))
            shape.SetEnd(point(*end))
            shape.SetLayer(pcbnew.Dwgs_User)
            shape.SetWidth(pcbnew.FromMM(0.15))
            self.board.Add(shape)
        text = pcbnew.PCB_TEXT(self.board)
        text.SetText(f"{ref} reserved: see design.UNSPECIFIED")
        text.SetPosition(point(x, y))
        text.SetLayer(pcbnew.Cmts_User)
        text.SetTextSize(pcbnew.VECTOR2I_MM(1.0, 1.0))
        self.board.Add(text)
        self.courtyards.append((ref, left, top, right, bottom))

    def outline(self, rectangle):
        left, top, right, bottom = rectangle
        corners = [(left, top), (right, top), (right, bottom), (left, bottom),
                   (left, top)]
        for start, end in zip(corners, corners[1:]):
            shape = pcbnew.PCB_SHAPE(self.board)
            shape.SetShape(pcbnew.SHAPE_T_SEGMENT)
            shape.SetStart(point(*start))
            shape.SetEnd(point(*end))
            shape.SetLayer(pcbnew.Edge_Cuts)
            shape.SetWidth(pcbnew.FromMM(0.1))
            self.board.Add(shape)

    def zone(self, net, layer, rectangle, priority=0):
        """One poured rectangle.

        `priority` exists for the L the southern MDGND is poured as. **Two
        zones of one net that overlap at the same priority are a DRC error**
        -- `zones_intersect`, "intersecting zones must have distinct
        priorities" -- and KiCad is right to insist: with equal priority the
        filler has no rule for which one owns the shared copper. Same net or
        not, the overlap has to be ordered.
        """
        left, top, right, bottom = rectangle
        item = pcbnew.ZONE(self.board)
        item.SetLayer(layer)
        item.SetNet(self.net(net))
        item.SetAssignedPriority(priority)
        item.SetLocalClearance(pcbnew.FromMM(CLEARANCE_MM))
        item.SetMinThickness(pcbnew.FromMM(0.2))
        outline = item.Outline()
        outline.NewOutline()
        for x, y in ((left, top), (right, top), (right, bottom), (left, bottom)):
            outline.Append(pcbnew.FromMM(float(x)), pcbnew.FromMM(float(y)))
        self.board.Add(item)
        return item

    def pad_boxes(self):
        """{net: [(x, y, half_width, half_height, layers)]} for the router.

        **From GetBoundingBox(), not from GetSize(), and the difference is a
        rotation.** GetSize() reports the pad in the footprint's own frame, so
        a SOIC-14 turned 90 degrees hands back 1.95 x 0.6 for a pad that is
        0.6 x 1.95 on the board. The router blocked the wrong rectangle, and
        the tracks it drew ran exactly along the rows of pad edges it thought
        were 0.675 mm further away: 199 shorts and 500 clearance violations
        from one axis swap. A bounding box is in board coordinates by
        construction and cannot be got round the wrong way.

        Copper with no net -- a spare section's pin, a mounting pad -- goes in
        under the empty name, which route_all() treats as hard. It routes to
        nothing and blocks everything.
        """
        boxes = {}
        for ref, footprint in self.footprints.items():
            for pad in footprint.Pads():
                key = (ref, pad.GetNumber())
                box = pad.GetBoundingBox()
                left, top = pcbnew.ToMM(box.GetLeft()), pcbnew.ToMM(box.GetTop())
                right = pcbnew.ToMM(box.GetRight())
                bottom = pcbnew.ToMM(box.GetBottom())
                # A through-hole pad is copper on every layer; an SMD pad is
                # copper on whichever layers it is *on*. The router needs to
                # know which, because it is what decides whether reaching that
                # pad costs a via -- and, for the QFN, whether the back side is
                # free.
                #
                # **This asked the drill and assumed the rest, and a QFN's
                # thermal pad is the case where that is wrong.** KiCad's
                # _ThermalVias variants put the exposed pad on F.Cu *and* on
                # B.Cu, so pad 57 of U19 is 3.2 mm square of ground on the back
                # of the board -- and declared as front-only it was invisible
                # to the router, which laid IRQ straight across it. DRC found
                # it 64 times. The pad knows what layers it is on; asking it is
                # both shorter and true of parts nobody has fitted yet.
                if pad.GetDrillSize().x > 0:
                    layers = LAYERS
                else:
                    layers = tuple(
                        side for side, copper in ((FRONT, pcbnew.F_Cu),
                                                  (BACK, pcbnew.B_Cu))
                        if pad.IsOnLayer(copper))
                boxes.setdefault(self._owner.get(key, ""), []).append(
                    ((left + right) / 2, (top + bottom) / 2,
                     (right - left) / 2, (bottom - top) / 2, layers))
        return boxes

    @staticmethod
    def _merge_collinear(points):
        """Drop the interior points of every straight run.

        **It does nothing today and that is worth saying rather than
        discovering.** It existed because route.py thought in cells and KiCad
        thinks in segments: the router returned a run as one point per grid
        cell, so a straight 9 mm run arrived as twenty 0.45 mm segments and
        dragging it in KiCad moved one cell. The first seed wrote 31,218
        segments of which 31,218 were one grid pitch long.

        With the router deleted, the one caller left is stitch_grounds(), and
        it hands over a two-point stub from a ground pad to its via -- so the
        guard below returns on every call this file makes. It is kept because
        it is correct and general and track() is the place a polyline would
        arrive if anything ever laid one, not because anything needs it now.
        """
        if len(points) < 3:
            return points
        kept = [points[0]]
        for before, here, after in zip(points, points[1:], points[2:]):
            if ((here[0] - before[0]) * (after[1] - here[1])
                    != (here[1] - before[1]) * (after[0] - here[0])):
                kept.append(here)
        kept.append(points[-1])
        return kept

    def track(self, net, layer, points, width=None):
        points = self._merge_collinear(points)
        for start, end in zip(points, points[1:]):
            item = pcbnew.PCB_TRACK(self.board)
            item.SetStart(point(*start))
            item.SetEnd(point(*end))
            item.SetWidth(pcbnew.FromMM(width or TRACK_MM))
            item.SetLayer(layer)
            item.SetNet(self.net(net))
            self.board.Add(item)

    def via(self, net, x, y):
        item = pcbnew.PCB_VIA(self.board)
        item.SetPosition(point(x, y))
        item.SetWidth(pcbnew.FromMM(VIA_DIAMETER_MM))
        item.SetDrill(pcbnew.FromMM(VIA_DRILL_MM))
        item.SetNet(self.net(net))
        item.SetViaType(pcbnew.VIATYPE_THROUGH)
        self.board.Add(item)

    def stitch_grounds(self):
        """A via beside every ground pad, down to the plane it belongs to.

        **The two grounds are not routed and must not be.** They are poured on
        both inner layers, so what a ground pad needs is not a track to another
        pad but a hole to the plane underneath it -- 104 pads, 104 vias, and no
        copper on the signal layers at all. Routing them instead would be a
        hundred tracks doing worse what a plane does perfectly, and every one
        of them would be a slot in the reference for the tracks that cross it.

        Three rules, and each of them is a DRC violation that happened:

        **Outward along the pad's long axis.** A pad sticks out of its body
        along its own length -- true of an 0805 and of a SOIC pin alike -- so
        that is the direction with nothing in it. Offsetting along the *body*
        axis instead sent the SSI2164's ground stub 1.1 mm sideways into its
        own V+ pin, twice.

        **The spot has to be clear of every other pad**, which is checked
        rather than assumed: the first candidate that clears everything by the
        hole clearance wins, and there are eight of them before this gives up.
        A via 0.8 mm off C711's ground pad is 0.15 mm off C712's rail pad, and
        the row is 3.5 mm apart.

        **The via has to land in its own pour.** A part that straddles the
        ground split -- the '541 and the three bypass relays do, by design --
        has analogue pins sitting over the digital plane, and a via there
        connects to nothing at all. So the spot is pulled back across the line
        into the zone that belongs to it, and the stub gets longer. That is
        what a straddling part costs, and it is cheaper than the alternative,
        which is a ground pin connected to the wrong ground.
        """
        placed, obstacles = 0, []
        # **A pad with a barrel *inside its own copper* is already stitched,
        # and this is the QFN's exposed pad.** The rule below skips a drilled
        # pad because its barrel crosses every layer; a QFN's thermal pad is an
        # SMD pad with drilled pads sitting inside it -- KiCad's _ThermalVias
        # variants are built exactly that way -- so the same argument applies
        # to it. Without this the build stops on U19.57, correctly: there is
        # nowhere beyond a 3.2 mm pad in the middle of a 56-pin package that is
        # not inside a pin row.
        #
        # **The test is overlap and not the pad number, and the difference is a
        # USB connector.** The first version of this asked whether any drilled
        # pad shared the number -- true of a thermal pad, and also true of the
        # micro-B's shield, which has four through-hole pegs and five SMD tabs
        # all numbered "SH" in different places. Two of those tabs then got no
        # stitch and no copper, and DRC reported J14's shield as unconnected to
        # itself. Same number is not same copper; overlapping boxes are.
        barrels = {}
        for ref, footprint in self.footprints.items():
            for pad in footprint.Pads():
                if pad.GetDrillSize().x > 0:
                    barrels.setdefault(ref, []).append(pad.GetBoundingBox())

        def has_barrel(ref, pad):
            box = pad.GetBoundingBox()
            return any(box.Intersects(other) for other in barrels.get(ref, ()))
        boxes = [(x, y, half_w, half_h)
                 for entries in self.pad_boxes().values()
                 for x, y, half_w, half_h, _ in entries]
        keep = VIA_DIAMETER_MM / 2 + 0.25
        # **And the stitches already laid, which this did not look at.** Every
        # candidate was tested against the *pads* and against nothing else, so
        # two neighbouring parts whose ground pads face each other could both
        # stitch into the same gap: DRC found two MAGND vias 0.25 mm apart on
        # a 0.30 mm drill -- overlapping holes, on a rule that has been in
        # force at every hole clearance this board has ever declared.
        #
        # It survived because the collision needs two pads close enough to
        # share a landing spot and far enough apart that neither pad blocks
        # the other's candidate, which is a window a placement falls into
        # rather than a state it tends to. Packing the bypass field one gap
        # east of the ground star was enough to find it.
        #
        # **Two distances and the net decides which**, because the two rules
        # this is between are of different kinds. Two vias on *different* nets
        # need the copper rule, rules.via_exclusion()["to_via_mm"] -- which is
        # what the router keeps and is 0.9 mm here. Two vias on the *same* net
        # have no clearance to keep at all and still have two drills: that is
        # the hole rule, and it is what DRC reported against the pair 0.25 mm
        # apart. Using the copper figure for both would be 0.2 mm of margin
        # invented on a rule that does not exist, and the bypass field is
        # packed tightly enough that inventing it costs a stitch.
        cross_keep = rules.via_exclusion()["to_via_mm"]
        same_keep = VIA_DRILL_MM + rules.hole_rules()["min_hole_to_hole"]
        laid_vias = []
        for ref, footprint in self.footprints.items():
            for pad in footprint.Pads():
                key = (ref, pad.GetNumber())
                net = self._owner.get(key)
                if net not in ("MAGND", "MDGND"):
                    continue
                # **A through-hole pad is already stitched.** Its barrel
                # crosses every layer, so the plane connects to it natively and
                # a via beside it is a second hole 0.8 mm from the first --
                # which is a hole-to-hole violation, not a connection.
                if pad.GetDrillSize().x > 0 or has_barrel(ref, pad):
                    continue
                position = pad.GetPosition()
                box = pad.GetBoundingBox()
                x, y = pcbnew.ToMM(position.x), pcbnew.ToMM(position.y)
                width = pcbnew.ToMM(box.GetWidth())
                height = pcbnew.ToMM(box.GetHeight())
                body = footprint.GetPosition()
                dx, dy = x - pcbnew.ToMM(body.x), y - pcbnew.ToMM(body.y)

                # **Off the pad's own long end first, and across it if that
                # is full.** A chip pad is longer across the body than along
                # it, so its long axis points into open board and the short
                # one points at the next part in the row -- which is why the
                # long axis is tried first and why it was, for four passes,
                # the only axis tried at all.
                #
                # **That failed on the first board where a row was packed to
                # its assembly gaps.** placement.pack_east() lays the supply
                # row at GAP_MM, and 0.6 mm between an 0805 and a 1210 is an
                # iron's clearance, not a via's: C811's MDGND pad wanted 3.9
                # mm of clear x between R804 and R805 and had 3.15, so all
                # three reaches on both directions landed inside a neighbour's
                # halo and the build stopped. Across the pad instead, the same
                # via is 0.8 mm south of the capacitor in empty board.
                #
                # **Reach is the outer loop and axis the inner**, so a short
                # stub across the pad beats a long one off its end. The
                # preference is about which way is usually clear; the stub's
                # length is inductance.
                if height >= width:
                    long_axis, long_half, long_delta = "y", height / 2, dy
                    across, across_half, across_delta = "x", width / 2, dx
                else:
                    long_axis, long_half, long_delta = "x", width / 2, dx
                    across, across_half, across_delta = "y", height / 2, dy

                spot, tried = None, []
                for reach in (0.9, 1.3, 1.7):
                    for axis, half, delta in ((long_axis, long_half,
                                               long_delta),
                                              (across, across_half,
                                               across_delta)):
                        sign = 1.0 if delta >= 0 else -1.0
                        for direction in (sign, -sign):
                            step = direction * (half + reach)
                            candidate = ((x + step, y) if axis == "x"
                                         else (x, y + step))
                            candidate = self._in_pour(net, candidate)
                            blocker = self._stitch_blocker(
                                candidate, net, boxes, keep, laid_vias,
                                same_keep, cross_keep)
                            if blocker is None:
                                spot = candidate
                                break
                            tried.append((candidate, blocker))
                        if spot:
                            break
                    if spot:
                        break
                if spot is None:
                    # **The candidates and what stopped each, because "move
                    # the part" is not actionable without them.** The first
                    # version of this message named the pad and nothing else,
                    # and the two placements that hit it both took a probe
                    # script to diagnose -- on a build that already knew the
                    # answer and was throwing it away.
                    detail = "\n  ".join(
                        f"({x:.2f}, {y:.2f}) -> {why}" for (x, y), why in tried)
                    raise SystemExit(
                        f"nowhere to stitch {ref}.{pad.GetNumber()} ({net}) "
                        f"-- every candidate on both axes is blocked. Move "
                        f"the part in placement.py:\n  {detail}")
                self.via(net, *spot)
                self.track(net, pcbnew.F_Cu, [(x, y), spot])
                laid_vias.append((spot, net))
                placed += 1
                # Both the via and the stub are copper the router has to see.
                # The via is through-plated so it blocks both signal layers;
                # the stub is on F.Cu alone, and saying so is worth 104 pieces
                # of back-side routing space.
                obstacles.append((LAYERS, spot[0], spot[1],
                                  VIA_DIAMETER_MM / 2, VIA_DIAMETER_MM / 2))
                obstacles.append((
                    (FRONT,), (x + spot[0]) / 2, (y + spot[1]) / 2,
                    abs(spot[0] - x) / 2 + TRACK_MM / 2,
                    abs(spot[1] - y) / 2 + TRACK_MM / 2))
        return placed, obstacles

    @staticmethod
    def _stitch_blocker(spot, net, boxes, keep, laid, same_keep, cross_keep):
        """What stops a via here, as a sentence, or None if nothing does."""
        x, y = spot
        for px, py, half_w, half_h in boxes:
            if (abs(x - px) < half_w + keep and abs(y - py) < half_h + keep):
                return (f"pad copper at ({px:.2f}, {py:.2f}), "
                        f"{max(abs(x - px) - half_w, abs(y - py) - half_h):.2f}"
                        f" mm against {keep:.2f}")
        for other, other_net in laid:
            need = same_keep if other_net == net else cross_keep
            gap = math.dist(spot, other)
            if gap < need - 1e-9:
                return (f"the stitch at ({other[0]:.2f}, {other[1]:.2f}) on "
                        f"{other_net}, {gap:.2f} mm against {need:.2f}")
        return None

    @staticmethod
    def _in_pour(net, spot):
        """Pull a stitch spot back across the ground split into its own zone."""
        x, y = spot
        edge = placement.GROUND_GAP / 2 + 0.6
        if net == "MAGND" and y > placement.SPLIT_Y - edge:
            return (x, placement.SPLIT_Y - edge)
        if net == "MDGND" and y < placement.SPLIT_Y + edge:
            return (x, placement.SPLIT_Y + edge)
        # And the second MDGND rectangle, which is the supply band east of the
        # isolation line. A stitch anywhere in the primary's quadrant would
        # land on no plane at all -- the same fault J8's own note records, one
        # boundary later.
        if (net == "MDGND" and y > placement.ISOLATION_Y - edge
                and x < placement.ISOLATION_X + placement.ISOLATION_STITCH_MM):
            return (placement.ISOLATION_X + placement.ISOLATION_STITCH_MM, y)
        return spot

    def fill(self):
        filler = pcbnew.ZONE_FILLER(self.board)
        filler.Fill(self.board.Zones())

    def rules(self):
        settings = self.board.GetDesignSettings()
        settings.SetCopperLayerCount(4)
        settings.m_TrackMinWidth = pcbnew.FromMM(TRACK_MM)
        settings.m_ViasMinSize = pcbnew.FromMM(VIA_DIAMETER_MM)
        settings.m_MinClearance = pcbnew.FromMM(CLEARANCE_MM)
        settings.m_CopperEdgeClearance = pcbnew.FromMM(EDGE_CLEARANCE_MM)
        # The two hole rules, set here as well as written by gen_project.py
        # for the reason every other rule is: SaveBoard() serialises what the
        # board carries, and this file re-runs gen_project.py afterwards so
        # the project keeps them. rules.hole_rules() owns the choice -- see
        # its comment for why PCBWay's hole-to-hole is the stricter of the two
        # sources and its hole-to-copper is not.
        holes = rules.hole_rules()
        settings.m_HoleToHoleMin = pcbnew.FromMM(holes["min_hole_to_hole"])
        settings.m_HoleClearance = pcbnew.FromMM(holes["min_hole_clearance"])

    def save(self, path):
        self.board.BuildListOfNets()
        pcbnew.SaveBoard(str(path), self.board)


def check_courtyards(board):
    """placement.SIZE agrees with the footprints KiCad actually loaded.

    **This file is the only place the two exist at once**, which is exactly why
    they were allowed to disagree. placement.py cannot import pcbnew -- that is
    the rule that keeps its arithmetic checkable -- so it carries a table of
    courtyard sizes, and that table had every multi-pin package transposed:
    SOIC-14 at (9.2, 6.6) against KiCad's 7.40 x 9.16, the 1x05 header at
    (13.4, 6.2) against 3.54 x 13.70.

    Nothing caught it because every consumer was transposed in the same way.
    check_overlaps() compares those boxes to each other, so two parts modelled
    sideways collide with each other just as they would upright; the board's
    own outline came from KiCad's boxes here and placement.main() printed a
    different one from the table, and the two numbers were 8 mm apart in
    print, on two lines of the same build log, for as long as the board has
    existed.

    KiCad's BBox() includes the courtyard line, and placement.SIZE is the
    outline centreline, so the model is expected to sit *inside* the bounding
    box by placement.COURTYARD_TOLERANCE_MM on each edge -- and by no more,
    which is the half that makes this a check rather than a bound.
    """
    problems = []
    allowed = placement.COURTYARD_TOLERANCE_MM
    for ref, left, top, right, bottom in board.courtyards:
        if ref in RESERVED_MM:
            continue
        modelled = placement.courtyard(ref)
        if modelled is None:
            problems.append(f"{ref} has a footprint and no entry in "
                            f"placement.SIZE")
            continue
        for name, mine, theirs, sign in (("left", modelled[0], left, 1),
                                         ("top", modelled[1], top, 1),
                                         ("right", modelled[2], right, -1),
                                         ("bottom", modelled[3], bottom, -1)):
            inset = sign * (mine - theirs)
            if not 0.0 <= inset <= allowed:
                problems.append(
                    f"{ref}: placement.py puts the {name} courtyard edge at "
                    f"{mine:.3f} and KiCad's footprint at {theirs:.3f}, "
                    f"{inset:+.3f} mm inside it against an allowance of "
                    f"0 to {allowed} -- check the SIZE entry, and check it is "
                    f"not on the wrong axis")
    return problems



def build():
    # Before anything is placed: does the board on disk have copper on it that
    # a person drew? gen_pcb_guard.refuse_to_discard_routing() is the rule and
    # it lives in its own file so test_verify.py can exercise it without
    # KiCad -- this is the first thing that happens, because everything after
    # it is unrecoverable.
    gen_pcb_guard.refuse_to_discard_routing(BOARD)
    # Then: the rules this board is about to be built to are inside what the
    # fabricator publishes. Cheap, and it fails at the top rather than at DRC.
    rules.check_fab_class()
    board = Board()
    board.rules()

    for ref in sorted(circuit.PARTS, key=lambda r: (r[0], len(r), r)):
        spot = placement.position(ref)
        if spot is None:
            raise SystemExit(f"{ref} has no position -- see placement.py")
        x, y, rotation = spot
        if ref in RESERVED_MM:
            board.reserve(ref, x, y, *RESERVED_MM[ref])
        else:
            board.place(ref, x, y, rotation)

    mismatched = check_courtyards(board)
    if mismatched:
        raise SystemExit("placement.SIZE disagrees with KiCad's footprints:\n  "
                         + "\n  ".join(mismatched[:8]))

    # **The refs go with the boxes, because placement.EDGE_PARTS needs them.**
    # A connector that mates with a cable contributes to the outline without
    # the margin every other part gets, and without the reference this call
    # cannot tell which is which -- which is exactly the bug it had: a board
    # 5 mm wider than placement.py's own report, with the USB receptacle
    # 5 mm inside an edge it is supposed to be flush with.
    rectangle = placement.extents(board.courtyards)
    board.outline(rectangle)

    # The two grounds, on both inner layers, with placement.GROUND_GAP between
    # them. Two zones on one layer with different nets fill straight through
    # each other and DRC does not object -- each is correctly connected to its
    # own net -- so the separation is geometric and verify.py is what holds it.
    left, top, right, bottom = rectangle
    inset = 0.5
    split = placement.SPLIT_Y
    half = placement.GROUND_GAP / 2
    # **MDGND is two rectangles and not one, and the second one is the
    # isolation barrier expressed as an absence.** The supply's primary side
    # is referenced to IGND -- the inlet's own 0 V, which through the shared
    # barrel jack is the mixer's PGND -- and a ground plane running under it
    # would be a plate capacitor across the barrier at exactly the frequency
    # design.barrier_return() is trying to keep out of the audio bond. So the
    # southern pour stops at placement.ISOLATION_Y across the primary's half
    # of the board and resumes east of placement.ISOLATION_X.
    #
    # There is no third zone for IGND. A pour would be the obvious thing and
    # it is wrong here for the same reason: it is 300 mm2 of copper facing the
    # MDGND plane on the layer above, which is the coupling the gap exists to
    # remove. Seven pins of primary is a routed net.
    iso_x = placement.ISOLATION_X
    iso_y = placement.ISOLATION_Y
    iso_south = placement.isolation_south()
    for layer in (pcbnew.In1_Cu, pcbnew.In2_Cu):
        board.zone("MAGND", layer,
                   (left + inset, top + inset, right - inset, split - half))
        board.zone("MDGND", layer,
                   (left + inset, split + half, right - inset, iso_y - half))
        # **The second rectangle starts at the split and not at the isolation
        # line, and the difference is one unconnected item.** Drawn as two
        # abutting-but-not-touching rectangles -- north part down to iso_y,
        # south part from iso_y -- MDGND becomes two *islands* with a 2 mm gap
        # between them, and KiCad is right to call that a missing connection:
        # a plane in two pieces is two planes. Overlapping them into an L
        # instead costs nothing, because the overlap is copper on the same net,
        # and it leaves exactly the corner that has to be empty empty.
        #
        # It cost a build to find, and what found it was DRC's unconnected
        # count rather than anything here -- which is the argument for
        # verify.UNROUTED_ITEMS being zero rather than small.
        board.zone("MDGND", layer,
                   (iso_x + half, split + half, right - inset,
                    bottom - inset), priority=1)
        # **The third rectangle, and its absence left the module over bare
        # laminate.** The two above make an L whose inside corner is the
        # primary's, and with no southern edge to that corner the bare region
        # ran to the bottom of the board -- which stopped being the supply
        # row's own band the moment the Pico got a strip below it. D806 and
        # the western third of U19 sat over no plane at all, and
        # check_isolation_gap() reported their copper as *inside the
        # primary's region*, which was true of the region as written.
        # placement.isolation_south() is the edge; this is the pour that
        # follows it, and the three overlap into a C rather than abutting for
        # the reason the second one overlaps the first.
        # Priority 2 and not 1: two zones on one layer at the same priority
        # is `zones_intersect` to DRC, whatever net they are on. The northern
        # pair get away with 0 and 1; this one overlaps the second, so it
        # needs a third number. Nothing about the fill changes -- they are the
        # same net and the priority only orders who yields to whom.
        board.zone("MDGND", layer,
                   (left + inset, iso_south + half, right - inset,
                    bottom - inset), priority=2)

    stitched, _stitch_copper = board.stitch_grounds()

    board.fill()
    OUT.mkdir(exist_ok=True)
    board.save(BOARD)
    return board, rectangle, stitched


def main():
    board, rectangle, stitched = build()
    left, top, right, bottom = rectangle
    width, height = right - left, bottom - top
    print(f"{BOARD.name}: {len(board.footprints)} footprints, "
          f"{len(RESERVED_MM)} reserved, {len(board.nets)} nets")
    print(f"  outline {width:.1f} x {height:.1f} mm = {width * height:.0f} mm2, "
          f"four layers, ground split at y = {placement.SPLIT_Y:.1f}")
    print(f"  {stitched} ground pads stitched to the planes")
    print("  no signal copper: place and pour only. Route it with krt.py, or "
          "in KiCad by hand.")
    print("  ** re-running this file discards hand-routed copper. To move a "
          "netlist change onto a routed board, use KiCad's Update PCB from "
          "Schematic against out/cv-module.kicad_sch. **")


if __name__ == "__main__":
    main()
