pythagorean-comma/cv-module/verify.py

"""Read the schematic back through KiCad and check it against section 5.

The five constraints in `hardware-spec-v0.md` section 5 are described there as
load-bearing rather than stylistic, and CLAUDE.md says to check them
mechanically rather than by eye. This is that check.

**What it reads changed, and that change is the point of the exercise.** This
file used to read `out/cv-module.net`, written by gen_netlist.py from the same
`design.py` these checks import. Every check passed and none of them could ever
have failed for a transcription error, because there was no transcription: the
comparison was design.py against itself, laundered through a file. What it
caught was a design that violates its own constraints, which is worth having and
is not what its docstring claimed.

It now runs

    kicad-cli sch export netlist --format kicadsexpr

over `out/cv-module.kicad_sch` and reads that. Every net in it was formed by
*KiCad* out of geometry -- wire ends meeting at coordinates, pins landing
mid-wire, labels naming what they touch -- so a route that misses its target by
1.27 mm now changes the answer. That is the whole argument for synthesising a
schematic, it is what the mixer's own verify.py does, and it is the reason
`gen_sch.py` names every interior node: an unlabelled net comes out of the
export as `Net-(C141-Pad1)`, which compares by node-set and never tells you
which net moved.

`out/from-kicad.net` is a build artefact and is regenerated on every run.
`out/cv-module.net` is still written by gen_netlist.py and is still the file the
BOM and the floorplan read; it is no longer what this file checks.

What it catches:

  * a rail this module is forbidden to touch, appearing anywhere;
  * a second bond between the two grounds, which is what one stray ground
    symbol produces and what turns the star into six loops;
  * a shield landing anywhere but its own pin-3, or at both ends;
  * anything landing on SIN{n} that can put DC into the mixer's summing node;
  * a load at PIN{n} that is not the 10k the DC-block corner was computed for;
  * an audio conductor leaving the module without a declared pair and shield;
  * a pin left open on the sheet that the design has not declared open;
  * an envelope rectifier diode fitted backwards, which is the fault the mixer
    records twice and could not catch;
  * a bypass contact on the wrong pole, a coil that does not return to the one
    sink, or a servo sensing downstream of the changeover;
  * R_IN switched, loaded, revalued or no longer equal to R_OUT, which is what
    the coarse pad's deletion rests on -- see design.pad_benefit().

None of those is visible to ERC, to DRC, or to a netlist comparison against
design.py -- which is the test the mixer's own check_ground_star() docstring
applies, and the reason these are separate functions rather than assertions
buried in the generator.
"""

import json
import math
import pathlib
import subprocess
import sys

import design
import gen_project
import placement
import rules
import contract.socket as socket
from toolchain import kicad, kisim, sexp

OUT = pathlib.Path(__file__).resolve().parent / "out"
SHEET = OUT / "cv-module.kicad_sch"
NETLIST = OUT / "from-kicad.net"
ERC = OUT / "from-kicad-erc.json"
PROJECT = OUT / "cv-module.kicad_pro"
PCB = OUT / "cv-module.kicad_pcb"
DRC = OUT / "from-kicad-drc.json"


def export_netlist(schematic, destination):
    """Ask KiCad what the drawing means. Lifted from the mixer's verify.py.

    Regenerated every run rather than read from the tree, so the answer is
    always about the schematic on disk now. A stale export is the one way this
    check can go quiet without saying so.
    """
    if not schematic.exists():
        raise SystemExit(f"{schematic} does not exist -- run gen_sch.py")
    result = subprocess.run(
        [str(kicad.KICAD_CLI), "sch", "export", "netlist", "--format",
         "kicadsexpr", "-o", str(destination), str(schematic)],
        capture_output=True, text=True)
    if result.returncode != 0 or not destination.exists():
        raise SystemExit(
            f"netlist export failed:\n{result.stdout}\n{result.stderr}")
    return destination


# KiCad's own name for a pin that is on nothing. It emits one single-node net
# per open pin, so `unconnected-(U9-MODE-Pad1)` is not a net this design
# declares and is not a fault either -- it is the export's way of writing
# "open".
OPEN = "unconnected-"


def _nodes(net):
    """(ref, pin) for the real parts on one exported net.

    A `#PWR` or `#FLG` symbol names a net; it is not a part on it. The mixer's
    reader makes the same exclusion and KiCad already omits them, so this is
    belt and braces against a format that has changed before.
    """
    found = set()
    for node in sexp.find_all(net, "node"):
        ref = sexp.find(node, "ref")[1]
        if not ref.startswith("#"):
            found.add((ref, str(sexp.find(node, "pin")[1])))
    return found


def read_netlist(path):
    """net name -> set of (ref, pin), for the nets that are nets."""
    tree = sexp.parse(path.read_text())
    return {sexp.find(net, "name")[1]: _nodes(net)
            for net in sexp.find_all(sexp.find(tree, "nets"), "net")
            if not str(sexp.find(net, "name")[1]).startswith(OPEN)}


def read_open_pins(path):
    """The pins KiCad found on nothing, as a set of (ref, pin).

    Read separately from the nets rather than filtered out and forgotten,
    because it is the more interesting half of the export on a partial sheet:
    check_open_pins() holds it against design.py's own declaration, so KiCad
    and design.py have to agree about which pins are open and not merely about
    which are connected.
    """
    tree = sexp.parse(path.read_text())
    found = set()
    for net in sexp.find_all(sexp.find(tree, "nets"), "net"):
        if str(sexp.find(net, "name")[1]).startswith(OPEN):
            found |= _nodes(net)
    return found


def read_components(path):
    """reference -> value, from the emitted file."""
    tree = sexp.parse(path.read_text())
    out = {}
    for comp in sexp.find_all(sexp.find(tree, "components"), "comp"):
        out[sexp.find(comp, "ref")[1]] = sexp.find(comp, "value")[1]
    return out


def compare(actual, expected):
    """What KiCad found in the geometry is what design.py asked for, by name.

    **Compared by name, not by node-set, and the difference is the whole value
    of the change.** The node-set form -- match each net's frozenset of
    (ref, pin) and report the ones with no partner -- was what this file did
    while both sides came from design.py, and it survives a rename because it
    never reads the name. Against KiCad's export that is exactly the wrong
    trade: it reports "some net moved" twice, once as missing and once as
    unexpected, and leaves the reader to diff two sets of 500 nodes.

    By name, a wire that missed its endpoint says which net lost which pin. The
    price is that every net has to *have* a name on the sheet, which is why
    gen_sch.py labels the summing junctions and the integrator nodes that never
    leave their block. `Net-(C141-Pad1)` is what the alternative looks like, and
    it changes when a part is renumbered.

    Nets KiCad names for itself are reported separately: those are nets the
    geometry formed and design.py never declared, which is the shape of an
    accidental short between two things that were meant to be one node.
    """
    expected = {name: set(nodes) for name, nodes in expected.items()}
    problems = []
    for name in sorted(set(expected) - set(actual)):
        problems.append(
            f"{name} is in design.py and KiCad found no such net on the sheet")
    for name in sorted(set(actual) - set(expected)):
        problems.append(
            f"KiCad found net {name} = {sorted(actual[name])}, which design.py "
            f"does not declare")
    for name in sorted(set(actual) & set(expected)):
        if actual[name] == expected[name]:
            continue
        extra = sorted(actual[name] - expected[name])
        short = sorted(expected[name] - actual[name])
        problems.append(
            f"{name} carries {extra} that design.py does not put on it and is "
            f"missing {short}")
    return problems


# ---------------------------------------------------------------------------
# Section 5
# ---------------------------------------------------------------------------

def check_no_mixer_rail_load(nets):
    """1. The module draws nothing from VREG, V+ or V-.

    The parent document's reason: "Every mA on V- costs 65 mV of rail." The
    mixer's negative rail is a 55-ohm charge pump already sagging 0.47 V under
    its own op-amp, and NEGATIVE_RAIL_DROP is that figure.

    Two halves. The obvious one is that none of those nets appears here at all.
    The one worth writing is the second: this module's own rails must not be
    *named* the same as the mixer's, because a net called "V+" in both places
    is a check that passes by spelling. design.RAILS is deliberately VA+/VA-,
    and this asserts the two vocabularies stay disjoint.
    """
    problems = []
    for rail in socket.FORBIDDEN_RAILS:
        if rail in nets:
            problems.append(
                f"{rail} appears in this module's netlist, carrying "
                f"{sorted(nets[rail])} -- constraint 1 forbids drawing "
                f"anything from it")
    collisions = sorted(set(design.RAILS) & set(socket.FORBIDDEN_RAILS))
    if collisions:
        problems.append(
            f"this module's rail names collide with the mixer's: {collisions} "
            f"-- rename, or constraint 1 is enforced by spelling")
    return problems


def check_one_ground_bond(nets):
    """2a. Exactly one bond between module audio ground and board AGND.

    The mixer holds the same shape of rule with check_ground_star() and calls
    a second bridge "what a stray ground symbol on the wrong net produces". The
    consequence here is worse than there: a second bond does not merely make a
    loop inside one board, it makes a loop that encloses the mixer's AGND pour
    and the whole length of this module's loom.

    Also checks what else touches AGND, because a bond that is correct and a
    part hanging off the same net is the same fault arriving by a different
    route.
    """
    problems = []
    parts_on = {}
    for name, nodes in nets.items():
        for ref, _ in nodes:
            parts_on.setdefault(ref, set()).add(name)

    bridges = sorted(ref for ref, names in parts_on.items()
                     if {"MAGND", socket.AGND} <= names)
    if bridges != [design.GROUND_STAR]:
        problems.append(
            f"MAGND and {socket.AGND} are bridged by {bridges or 'nothing'}, "
            f"expected exactly ['{design.GROUND_STAR}'] -- constraint 2")

    allowed = {design.GROUND_STAR, "J7"}
    found = {ref for ref, _ in nets.get(socket.AGND, ())}
    if found != allowed:
        problems.append(
            f"{socket.AGND} carries {sorted(found)}, expected {sorted(allowed)} "
            f"-- the bond and the pad it leaves on, and nothing else")
    return problems


def check_module_star(nets):
    """Exactly one part bridges MAGND and MDGND, and it is R902.

    **The module's own star, which had no check until a part arrived that
    could break it.** check_one_ground_bond() holds the bond to the *mixer*
    and constraint 5.2 is about that one; this is the boundary inside this
    board, the one floorplan.py's whole zone argument is built on, and until
    now nothing asserted it. It survived unasserted because no part had two
    ground pins: the '541 and the relays straddle the line in *signals*, and
    their grounds are all MAGND.

    The envelope ADC is the first part with an AGND pin and a DGND pin, and
    its own datasheet offers two ways to wire them. Section 7.3's first scheme
    -- two supplies, two grounds, joined at their own star -- is the textbook
    one and is wrong here, because this board already has a star and a second
    one is a second join between two domains. The second scheme, "consider the
    MCP3561/2/4 as an analog component, and therefore, connect AVDD to DVDD
    and AGND to DGND", is what design.envelope_adc() draws.

    **The fault it exists for draws correctly and measures correctly.** DGND
    to MDGND is what a careful person does with a pin called DGND; it looks
    tidier than the alternative, ERC is silent because both are ground nets,
    DRC is silent because both pours exist, and the board works. What it makes
    is a second conductor between the two returns, in parallel with R902 and
    tens of millimetres away from it -- so the two enclose a loop, and every
    milliamp of digital return current that finds it flows past six analogue
    channels on its way home. That is the failure the split exists to prevent,
    arriving through the one pin that invites it.
    """
    parts_on = {}
    for name, nodes in nets.items():
        for ref, _ in nodes:
            parts_on.setdefault(ref, set()).add(name)
    bridges = sorted(ref for ref, names in parts_on.items()
                     if {"MAGND", "MDGND"} <= names)
    if bridges == [design.DOMAIN_STAR]:
        return []
    return [f"MAGND and MDGND are bridged by {bridges or 'nothing'}, expected "
            f"exactly ['{design.DOMAIN_STAR}'] -- a second bridge is a loop "
            f"between the two returns, and floorplan.CROSSING_RULE is about "
            f"what may cross it, not about how many joins there are"]


def check_shield_returns(nets):
    """2b. Six separate returns to six pin-3s, not commoned in the module.

    **The clause this checks is not the one CLAUDE.md states, and the change is
    deliberate.** That sentence asked for six *conductors* carrying returns,
    and design.FRONT_R records the arithmetic that removed it: with a single
    bond carrying all six channels, pairwise crosstalk is 122 dB below one
    string on a 100 mm bond and 103 dB on a deliberately bad one, against a
    -54 dB requirement. Six return conductors have no mechanism here.

    What survives is the half that does: six *shields*, one per channel,
    landing on six separate pin-3s and grounded at the main-board end only.
    That is per-channel electrostatic separation in a loom that runs past a
    45 kHz charge pump, and it is what constraint 5 asks for independently.

    So this asserts the shields, and check_one_ground_bond() above asserts the
    single bond. Between them the two real properties of constraint 2 are held
    and the one with no mechanism is not.
    """
    problems = []
    for n in range(1, design.CHANNELS + 1):
        loom = design.LOOM[n]
        if loom["shield_pin"] != socket.PIN_RETURN:
            problems.append(
                f"channel {n}'s shield lands on socket pin "
                f"{loom['shield_pin']}, but the mixer at {socket.PIN[:7]} has "
                f"AGND on pin {socket.PIN_RETURN}")
        if socket.channel_socket(n).get(loom["shield_pin"]) != socket.AGND:
            problems.append(
                f"channel {n}'s shield pin is not AGND upstream")

    pins = [design.LOOM[n]["shield_pin"] for n in range(1, design.CHANNELS + 1)]
    if len(pins) != design.CHANNELS:
        problems.append("not six shields")

    # No return conductor may have crept back in: a net reaching a loom
    # connector must be one of that channel's two signals and nothing else.
    for n in range(1, design.CHANNELS + 1):
        found = {net for net, entries in design.NETS.items()
                 if any(ref == f"J{n}" for ref, _ in entries)}
        if found != set(design.LOOM[n]["conductors"]):
            problems.append(
                f"J{n} carries {sorted(found)}, expected "
                f"{sorted(design.LOOM[n]['conductors'])} -- a third conductor "
                f"in the loom is a second path to the mixer's ground")
    return problems


def check_sin_dc_by_construction(nets, values):
    """3. SIN{n} puts no more DC through the master wiper than the mixer does.

    **Restated in CLAUDE.md from "zero DC by construction", which overstated by
    three orders of magnitude.** The servo leaves 0.5 mV, which through C703 and
    R706 is 3.0 nA at the wiper against the 0.2-1.0 nA the mixer already accepts
    from U1B's own offset. See constraints.py.

    A netlist cannot measure volts, so what is checked is still the
    construction -- and **the construction moved when the bypass relay landed,
    so this check moved with it rather than being loosened to accommodate it.**
    SIN{n} used to be the I-V amplifier's own output. It is now the mixer's
    wiper on one side of a changeover contact, with the amplifier on the other:

        SIN{n}    the loom, and this channel's own relay pole
        IVOUT{n}  the I-V output, its feedback pair, the servo sense, and the
                  same relay's normally-open contact

    Anything additional on either is a path that can put DC into R{n}01 and
    from there into the mixer's summing node, where six channels' worth lands
    on the master pot's wiper.

    Two things are asserted that could not be before, and both are failures a
    drawing would not show.

    **The servo must sense IVOUT{n} and not SIN{n}.** Downstream of the contact
    the loop opens the moment the module leaves circuit, and an integrator with
    an open loop goes to a rail and stays there -- so the module would come
    back from bypass wrong rather than coming back. The old wiring is now a
    fault and test_verify.py plants it.

    **The pole must be this channel's own.** bypass_contact(n) says which, and
    a channel wired to a neighbour's pole is a board that bypasses two strings
    to one place and leaves another pair crossed. Every other instrument passes
    on it: the parts are all present, the counts are right, and ERC has nothing
    to say about which contact of a relay a net lands on.
    """
    problems = []
    for n in range(1, design.CHANNELS + 1):
        relay, com, nc, no = design.bypass_contact(n)
        for name, expected in (
                (f"SIN{n}", {f"J{n}", relay}),
                (f"IVOUT{n}", {f"R{n}21", f"C{n}21", f"R{n}31", relay,
                               design.SECTIONS[("iv", n)][0]})):
            found = {ref for ref, _ in nets.get(name, ())}
            if found != expected:
                problems.append(
                    f"{name} carries {sorted(found)}, expected "
                    f"{sorted(expected)} -- see design.fail_safe() for why "
                    f"the I-V output and the mixer's wiper are two nets")
            if design.net_dc(name) != (0.0, 0.0):
                problems.append(f"{name} is not declared 0 V DC in NET_DC")
        if (relay, com) not in nets.get(f"SIN{n}", ()):
            problems.append(
                f"SIN{n} is not on {relay}.{com}, which is the pole "
                f"design.bypass_contact({n}) assigns it")
        if (relay, no) not in nets.get(f"IVOUT{n}", ()):
            problems.append(
                f"IVOUT{n} is not on {relay}.{no} -- the module must reach the "
                f"wiper through the *normally open* contact, or de-energised "
                f"is not bypass")
        if (f"R{n}31", "1") not in nets.get(f"IVOUT{n}", ()):
            problems.append(
                f"channel {n}'s servo does not sense IVOUT{n} -- either the "
                f"VCA's own 150 nA offset current stands on the output, or "
                f"the loop is downstream of the bypass contact and opens "
                f"every time the module leaves circuit")
    return problems


def check_pin_load(nets, values):
    """4. PIN{n} presents 5-10 kohm, keeping the DC-block corner inside the
    15.9-31.8 Hz the fabricated design already sweeps.

    **Corrected in CLAUDE.md.** The old wording said "or the 31.8 Hz corner
    moves", and 31.8 Hz is the corner at 5 kohm -- one end of the window, so the
    sentence held at exactly one point in its own range. See constraints.py.

    Three claims, and the third is the one a netlist is uniquely able to make.

    The value is inside the window. The window is the mixer's own, and both
    ends of it are real: attenuator_input_impedance() is 10k with the pot shut
    and 5k wide open, so anything in between reproduces some position of the
    control this module replaces.

    Nothing else is on the node **except this channel's own bypass contact**. A
    second part at PIN{n} -- the 1 Mohm envelope tap spec section 4.1 puts here,
    for instance -- shifts the load and the corner with it, and the symptom is a
    tonal complaint rather than a fault.

    The contact is admitted rather than excused. It is open whenever the module
    is in circuit, so the 10.000 kohm above is what PIN{n} sees in normal
    operation; when it closes, PIN{n} and SIN{n} become one node and the mixer
    sees R{n}01 in parallel with its own RIN -- 5 kohm, which
    design.bypass_state() shows is exactly what the fabricated pot presents at
    full rotation. Both ends of the changeover are conditions the mixer was
    built for, and that is the argument for allowing the extra member here
    rather than the convenience of it.

    And the load is a resistor into a *virtual earth*, not a shunt to ground.
    That is what makes it 10.000 kohm rather than 10k in parallel with whatever
    the next stage's input happens to be, and it is checked by following
    R{n}01's far end to the front-end amplifier's inverting pin.
    """
    problems = []
    low, high = 5_000.0, 10_000.0
    for n in range(1, design.CHANNELS + 1):
        name = f"PIN{n}"
        relay, _, nc, _ = design.bypass_contact(n)
        expected = {f"J{n}", f"R{n}01", relay}
        found = {ref for ref, _ in nets.get(name, ())}
        if found != expected:
            problems.append(
                f"{name} carries {sorted(found)}, expected {sorted(expected)} "
                f"-- the loom, the socket load and this channel's own bypass "
                f"contact")
            continue
        if (relay, nc) not in nets.get(name, ()):
            problems.append(
                f"{name} is not on {relay}.{nc} -- the link back to the wiper "
                f"must be the *normally closed* contact, or the module fails "
                f"into silence rather than into bypass")
        if values.get(f"R{n}01") != design.FRONT_R:
            problems.append(
                f"R{n}01 is {values.get(f'R{n}01')!r}, expected "
                f"{design.FRONT_R!r}")
        if not low <= design.FRONT_R_OHMS <= high:
            problems.append(
                f"R{n}01 is {design.FRONT_R_OHMS:.0f} ohm, outside the "
                f"{low:.0f}-{high:.0f} window constraint 4 allows")
        # The far end must be the front end's inverting input.
        package, unit = design.SECTIONS[("front", n)]
        inverting = design.OPAMP_UNITS[unit][1]
        virtual_earth = {ref for ref, _ in nets.get(f"FEN{n}", ())}
        if (package, str(inverting)) not in nets.get(f"FEN{n}", set()):
            problems.append(
                f"R{n}01 does not reach {package}'s inverting input -- the "
                f"load is not a virtual earth and is therefore not exactly "
                f"{design.FRONT_R_OHMS:.0f} ohm")
        if virtual_earth != {f"R{n}01", f"R{n}02", package}:
            problems.append(
                f"FEN{n} carries {sorted(virtual_earth)} -- anything else on "
                f"the summing junction changes what PIN{n} sees")
    return problems
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
