pythagorean-comma/cv-module/gen_fab.py

"""The fabrication package: what a fabricator receives, and what it must not.

    python3 gen_fab.py            # write fab/
    python3 gen_fab.py --verify   # is the tracked package a package of the
                                  # tracked board?

**This file exists because a decision was taken, and it is worth writing down
which one.** `gen_plots.orderable()` has read the gate off `design.py` and
`verify.py` since it was written -- parts with no footprint, blocks not drawn,
connections not routed -- and it returns nothing now. That did not make a
fabrication package appear, and the previous pass was right that it should not:
what was left was not a gate but a choice, and the repository said so rather
than quietly acquiring a `fab/`. The choice has now been made.

**What a package is, and where the numbers come from.** Every argument below
comes from the file that already owns it -- the layer set from the board, the
class and the stackup from `rules.py`, the hole rules from `rules.hole_rules()`
-- and nothing here is typed a second time. Where a fabricator's convention is
involved, the convention is the sibling's, because `../summing-mixer` has
ordered boards and this repository has not:
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
